sjkelly/AMRI-Rice-201308-sjkelly/scripts/droplet_analysis/samples/ellipses_test/ellipses_processed.png

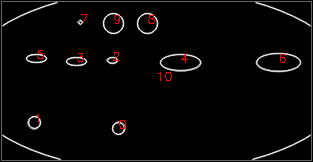
scripts/droplet_analysis/samples/ellipses_test/ellipses_processed.png
